ArashEM/VS-MP3/BOX/images/holder-1.jpg

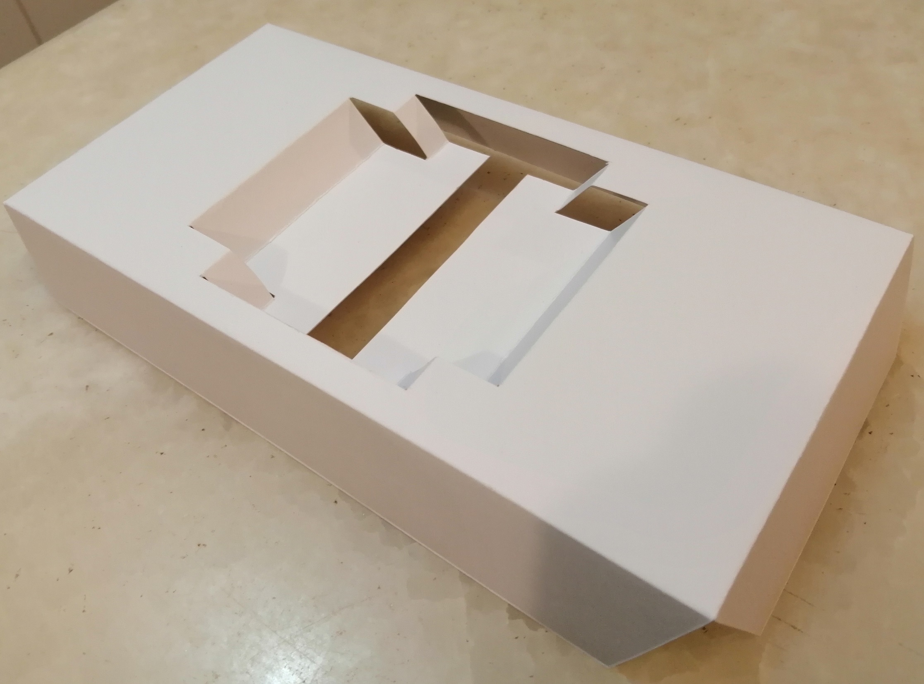
BOX/images/holder-1.jpg
