ArashEM/VS-MP3/BOX/images/image-3.jpg

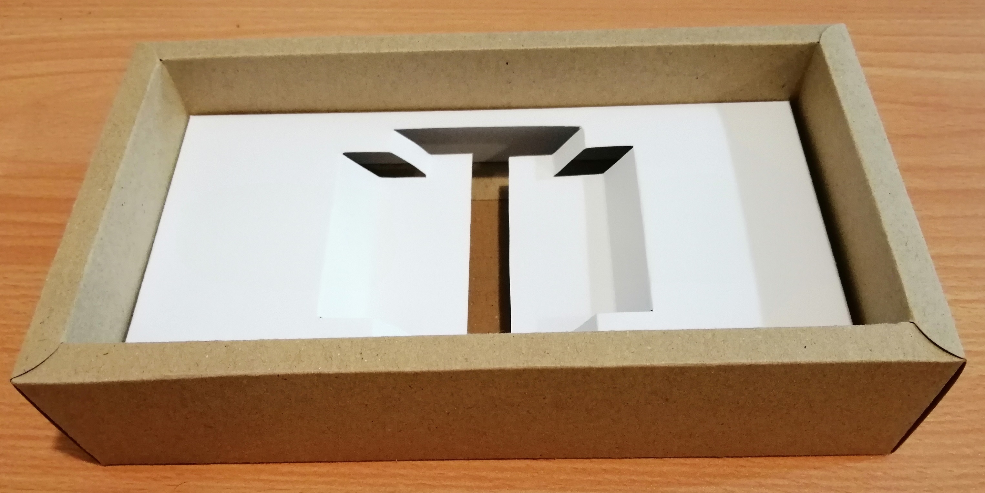
BOX/images/image-3.jpg
