ArashEM/VS-MP3/BOX/images/image-4.jpg

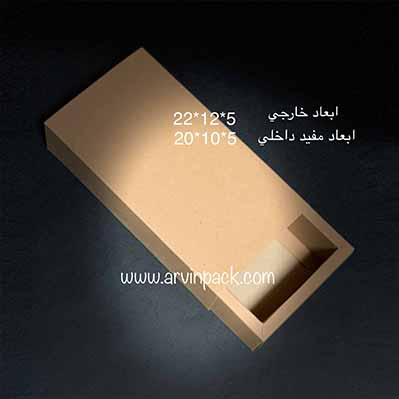
BOX/images/image-4.jpg
