ArashEM/VS-MP3/DOC/Pictures/IMAG1211.jpg

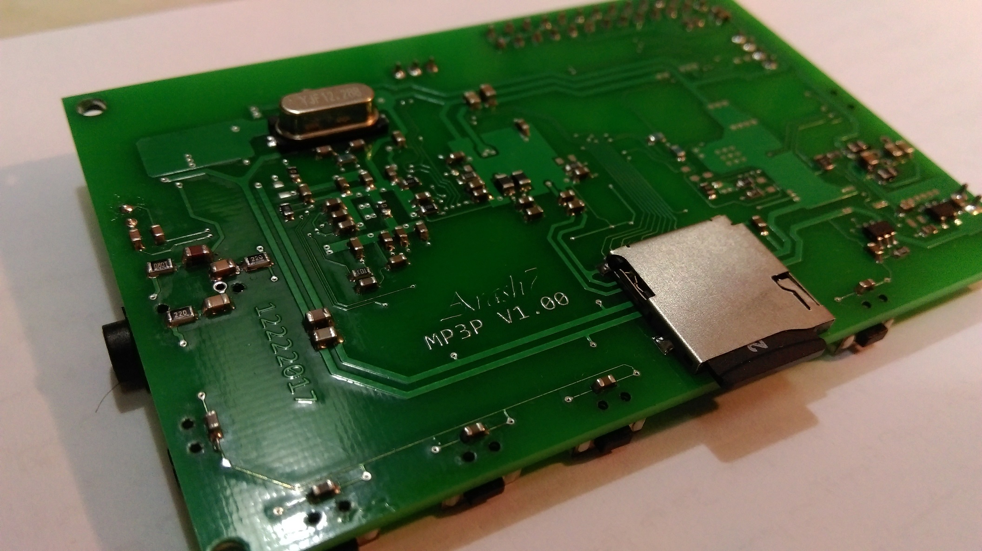
DOC/Pictures/IMAG1211.jpg
