ArashEM/VS-MP3/DOC/Pictures/IMAG1220.jpg

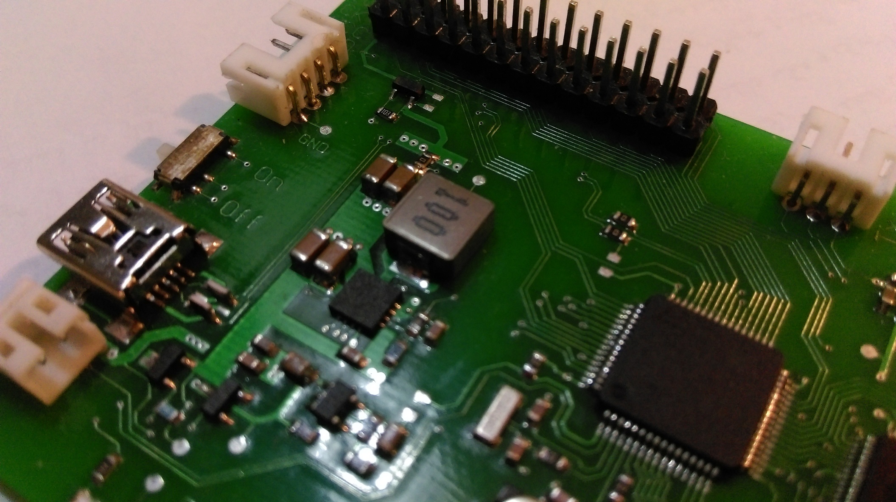
DOC/Pictures/IMAG1220.jpg
