ArashEM/VS-MP3/FW/Img/mountain.jpg

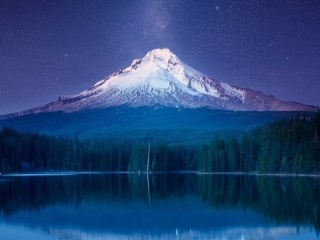
FW/Img/mountain.jpg
