ArashEM/VS-MP3/FW/Img/tired-owl.png

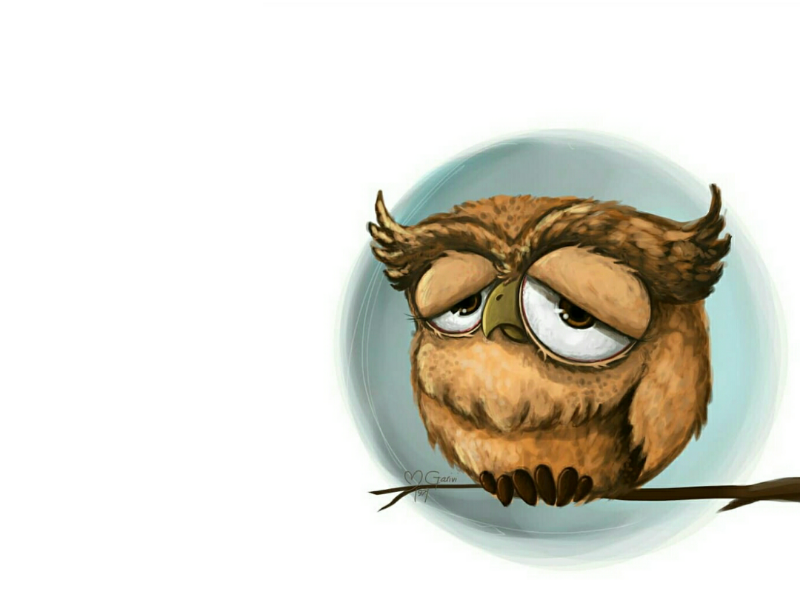
FW/Img/tired-owl.png
