ArashEM/VS-MP3/FW/Src/helper.c

/*****************************************************************************
  * @file    helper.c
  * @author  Arash Golgol
  * @brief   Helpers for MP3 player
*****************************************************************************/
/* FreeRTOS headers */
#include "FreeRTOS.h"
#include "task.h"
#include "queue.h"

/* HAL headers */

/* General headers */
#include <stdint.h>
#include "helper.h"
#include "mp3_player.h"
#include "vs10xx.h"
#include "debug.h"

/* Global variables */
static uint8_t								buff[STREAM_BUFF_SIZE];
#if (configUSE_TRACE_FACILITY == 1)
extern traceString 						sd_chn;	
#endif


/**
 * \brief           buffer event function
 */
static void sd_buff_evt_fn(lwrb_t* buff, lwrb_evt_type_t type, size_t len) {	
	struct stream_buff*		sbuff;
	struct mp3p_cmd 			sd_cmd;
	
	sbuff = container_of(buff, struct stream_buff, lwrb);
	
	switch (type) {
		case LWRB_EVT_RESET:
			break;
		
		case LWRB_EVT_READ:
#if (configUSE_TRACE_FACILITY == 1)
			vTracePrintF(sd_chn, "Buffer read event: %d byte(s)!\r\n", (int)len);
#endif
			if (lwrb_get_full(buff) < STREAM_BUFF_HALF_SIZE ) {
				/* we need more data in stream buffer */
				sd_cmd.cmd = CMD_SDCARD_CONT_READ;
				sd_cmd.arg = (uintptr_t) sbuff;
				xQueueSend(sbuff->qwrite, &sd_cmd, 0);
			}	 /* if (lwrb_get_full(buff) < STREAM_BUFF_HALF_SIZE ) */
		break;
    
		case LWRB_EVT_WRITE:
#if (configUSE_TRACE_FACILITY == 1)
			vTracePrintF(sd_chn, "Buffer write event: %d byte(s)!\r\n", (int)len);
#endif
		break;
    
		default: break;
	}
}

/**
 *	\brief	allocate stream buffer for playing 
 */
struct stream_buff*	sbuff_alloc(QueueHandle_t qw)
{
	struct stream_buff*				sbuff;
	
	/* initlizie file and stream buffer */
	sbuff = (struct stream_buff *)pvPortMalloc(sizeof(struct stream_buff));
	configASSERT(sbuff);
	sbuff->qwrite = qw;
	
	/* initlizie lwrb */
	//buff  = (uint8_t *)pvPortMalloc(STREAM_BUFF_SIZE);
	configASSERT(buff);
	lwrb_init(&sbuff->lwrb, buff, STREAM_BUFF_SIZE);
	lwrb_set_evt_fn(&sbuff->lwrb, sd_buff_evt_fn);
	
	return sbuff;
}

/**
 * \brief send required commands to start playing 
 */
void start_playing(	struct stream_buff* sbuff, 
										struct controller_qlist* qlist, 
										const char* file)
{
	struct mp3p_cmd						qcmd;
	FRESULT										result;
	
	/* controll input */
	configASSERT(sbuff);
	configASSERT(qlist);
	configASSERT(file);
	
	result = f_open(&sbuff->file, file, FA_READ);
	debug_print("f_open: %d\r\n",result);
	configASSERT(result == FR_OK);
	
	/* create SD card data stream buffer */
	qcmd.cmd = CMD_SDCARD_START_READ;
	qcmd.arg = (uintptr_t) sbuff;
	xQueueSend(qlist->sdcard, &qcmd, 0);
	
	/* start playing mp3 file */
	qcmd.cmd = CMD_VS10XX_PLAY;
	qcmd.arg = (uintptr_t) sbuff;
	xQueueSend(qlist->vs10xx, &qcmd, 0);
	
	/* blink while playing */
	qcmd.cmd = CMD_LED_BLINK_SET;
	qcmd.arg = 1000;
	xQueueSend(qlist->blink, &qcmd, 0);
	
	/* set file name in HMI */
	qcmd.cmd = CMD_HMI_SET_MSG;
	qcmd.arg = (uintptr_t) file;
	xQueueSend(qlist->hmi, &qcmd, 0);
	
	debug_print("start playing %s\r\n",file);
}

/**
 * \brief send required commands to stop palying
 */
void stop_playing(struct stream_buff* sbuff, struct controller_qlist* qlist)
{
	struct mp3p_cmd						qcmd;
	
	/* controll input */
	configASSERT(sbuff);
	configASSERT(qlist);
	
	/* close file*/
	f_close(&sbuff->file);
	
	/* create SD card data stream buffer */
	qcmd.cmd = CMD_SDCARD_STOP_READ;
	qcmd.arg = (uintptr_t) sbuff;
	xQueueSend(qlist->sdcard, &qcmd, 0);
	
	/* start playing mp3 file */
	qcmd.cmd = CMD_VS10XX_STOP;
	qcmd.arg = (uintptr_t) sbuff;
	xQueueSend(qlist->vs10xx, &qcmd, 0);
	
	/* blink while playing */
	qcmd.cmd = CMD_LED_BLINK_OFF;
	qcmd.arg = 0;
	xQueueSend(qlist->blink, &qcmd, 0);
	
	debug_print("stop playing\r\n");
}
		
/**
 * \brief set sound volume 
 */
void set_volume(struct controller_qlist* qlist, const uint8_t vol)
{
	struct mp3p_cmd						qcmd;
	portBASE_TYPE taskWoken = pdFALSE;
	
	/* controll input */
	configASSERT(qlist);
	
	/* set voluem */
	qcmd.cmd = CMD_VS10XX_SET_VOL;
	qcmd.arg = (uint32_t)vol;
	xQueueSendFromISR(qlist->vs10xx, &qcmd, &taskWoken);
	portEND_SWITCHING_ISR(taskWoken);
	
	/* debug */
	debug_print("set volume to %d\r\n",vol);
}

/**
 * \brief create MP3 player command queue 
 */
struct controller_qlist* vsmp3_create_queues(void)
{
	struct controller_qlist*		qlist;			/* queue list for all tasks */
	
	qlist = 
	(struct controller_qlist* )pvPortMalloc(sizeof(struct controller_qlist));
	configASSERT(qlist);
	
	/* create task command queue */
	qlist->blink  = xQueueCreate(2, sizeof(struct mp3p_cmd));
	qlist->vs10xx = xQueueCreate(2, sizeof(struct mp3p_cmd));
	qlist->sdcard = xQueueCreate(2, sizeof(struct mp3p_cmd));
	qlist->hmi = xQueueCreate(2, sizeof(struct mp3p_cmd));
	
	return qlist;
}

/**
 * \brief create MP3 player tasks
 */
void vsmp3_create_tasks(struct controller_qlist* qlist)
{
	BaseType_t									xstatus;
	
	configASSERT(qlist);
	
	/* create blink tasks */
	xstatus = 	xTaskCreate(vtask_blink, 
													"blink", 
													TASK_BLINK_STACK_SIZE, 
													qlist, 			/* command queue to blink task */
													TASK_BLINK_PRIORITY, 
													NULL);
	configASSERT(xstatus == pdPASS);
	
	/* create controller task */
	xstatus = 	xTaskCreate(vtask_controller,
													"controller",
													TASK_CONTROLLER_STACK_SIZE,
													qlist,		/* list of command queues to each tasks */				
													TASK_CONTROLLER_PRIORITY, 
													NULL);
	configASSERT(xstatus == pdPASS);
	
	/* create vs10xx task */
	xstatus = 	xTaskCreate(vtask_vs10xx,
													"vs10xx",
													TASK_VS10XX_STACK_SIZE,
													qlist,
													TASK_VS10XX_PRIORITY,
													NULL);
	configASSERT(xstatus == pdPASS);
	
	/* create sdcard streaming buffer task */
	xstatus = 	xTaskCreate(vtask_sdcard,
													"sdcard",
													TASK_SDCARD_STACK_SIZE,
													qlist,
													TASK_SDCARD_PRIORITY,
													NULL);
	configASSERT(xstatus == pdPASS);
	
	/* create HDMI controller task */
	xstatus = 	xTaskCreate(vtask_hmi,
													"hmi",
													TASK_HMI_STACK_SIZE,
													qlist,
													TASK_HMI_PRIORITY,
													NULL);
	configASSERT(xstatus == pdPASS);
}

/**
 * in case of change in system state
 */
void maintenance_mode(const char * message, struct controller_qlist* qlist)
{
	struct mp3p_cmd						qcmd;
	
	/* message on LCD */
	qcmd.cmd = CMD_HMI_SET_MSG;
	qcmd.arg = (uintptr_t) message;
	xQueueSend(qlist->hmi, &qcmd, 0);
	
	/* blink fast while  maintenance*/
	qcmd.cmd = CMD_LED_BLINK_SET;
	qcmd.arg = 200;
	xQueueSend(qlist->blink, &qcmd, 0);
	
	debug_print("%s\r\n", message);
	
	/* infinit loop*/
	for(;;) {
		vTaskDelay(pdMS_TO_TICKS(1000));
	} /* for(;;) */
}

/**
 *  Run time stack overflow checking is performed if
 *  configCHECK_FOR_STACK_OVERFLOW is defined to 1 or 2. This hook function is
 *  called if a stack overflow is detected.
 */
void vApplicationStackOverflowHook(xTaskHandle xTask, signed char *pcTaskName)
{
	debug_print("stack overflow on: %s\r\n", pcTaskGetName(xTask));
	debug_print("stack overflow on: %s\r\n", pcTaskName);
}

/* EOF */
