ArashEM/VS-MP3/FW/Src/retarget.c

/*
*		Send stdio data to uart1
*/
#include <stdio.h>
#include <stm32f1xx_hal.h>

extern UART_HandleTypeDef huart1;

int fputc(int ch, FILE *f)
{
		HAL_UART_Transmit(&huart1, (uint8_t *)&ch, 1, 0xFFFF);
		return ch;
}

int fgetc(FILE *f)
{
		char ch;
		HAL_UART_Receive(&huart1, (uint8_t *)&ch, 1, 0xFFFF);
		return (int)ch;
}
